ade-sede/ThumbsUp/src/movement.c

#include "header.h"
#include "MPU9150.h"
#include "movement.h"
#include "RN42.h"

extern struct s_accel g_calibration;
extern struct s_gravity g_accel;
extern struct s_gravity g_angle;

extern float g_accelR;
extern float g_wheel;

void    accel_to_angle_value() {
	/* accelometre value translate to g value between -/+2 */
	g_accel.accelX = TRANS_ACCEL_TO_G(g_calibration.accelX);
	g_accel.accelY = TRANS_ACCEL_TO_G(g_calibration.accelY);
	g_accel.accelZ = TRANS_ACCEL_TO_G(g_calibration.accelZ);

        /* Vector Acceleration R submitted to gravity */
	g_accelR = sqrt(powf(g_accel.accelX, 2.0) + powf(g_accel.accelY, 2.0) + powf(g_accel.accelZ, 2.0));

	/* Give angle in degrees of the vector */
	g_angle.accelX = acosf(g_accel.accelX/ g_accelR) * 57.2958;
	g_angle.accelY = acosf(g_accel.accelY/ g_accelR) * 57.2958;
	g_angle.accelZ = acosf(g_accel.accelZ/ g_accelR) * 57.2958;
}

/*	
 * This is the function that measures the forces present in the system, 	
 * during a no-move condition at the beginnig	
 * and shorter during execution	
 * We average those measures using calibration_sample_number samples	
 */

 void calibration(void) {	
	u16 count = 0;	
	struct s_accel sample_accel;
        LATBbits.LATB14 = 1;
 	while (count <= CALIBRATION_SAMPLE_NUMBER) {	
		memset(&sample_accel, 0, sizeof(struct s_accel));	
		read_accel(&sample_accel);	
		g_calibration.accelX += sample_accel.accelX;	
		g_calibration.accelY += sample_accel.accelY;	
		g_calibration.accelZ += sample_accel.accelZ;	
		++count;
	}	
 	g_calibration.accelX /= CALIBRATION_SAMPLE_NUMBER;	
	g_calibration.accelY /= CALIBRATION_SAMPLE_NUMBER;	
	g_calibration.accelZ /= CALIBRATION_SAMPLE_NUMBER;

        g_accel.accelX = TRANS_ACCEL_TO_G(g_calibration.accelX);
	g_accel.accelY = TRANS_ACCEL_TO_G(g_calibration.accelY);
	g_accel.accelZ = TRANS_ACCEL_TO_G(g_calibration.accelZ);
        LATBbits.LATB14 = 0;
}

void    sampling_acceleration_value() {
	u16 count = 0;
	struct s_accel sample;
        struct s_accel accel;

        memset(&accel, 0, sizeof(struct s_accel));
	/* SAMPLING */
	while (count <= AVERAGE_SAMPLE_NUMBER) {
		memset(&sample, 0, sizeof(struct s_accel));
		read_accel(&sample);
		accel.accelX += sample.accelX;
		accel.accelY += sample.accelY;
		accel.accelZ += sample.accelZ;
		++count;
	}
	/* Retrieving average */
	accel.accelX /= AVERAGE_SAMPLE_NUMBER;
	accel.accelY /= AVERAGE_SAMPLE_NUMBER;
	accel.accelZ /= AVERAGE_SAMPLE_NUMBER;

        /* giving value between -2 +2 */
	g_accel.accelX = TRANS_ACCEL_TO_G(accel.accelX);
	g_accel.accelY = TRANS_ACCEL_TO_G(accel.accelY);
	g_accel.accelZ = TRANS_ACCEL_TO_G(accel.accelZ);
}

void    angle_calculation(struct s_gravity *arcos){
//
//        float x = 0;
//        float y = 0;
//        float z = 0;

	g_accelR = sqrt(powf(g_accel.accelX, 2.0)+powf(g_accel.accelY, 2.0)+ powf(g_accel.accelZ, 2.0));

//        x = (g_accel.accelX - 1) * 9.81;
//        y = (g_accel.accelY - 1) * 9.81;
//        z = (g_accel.accelZ - 1) * 9.81;

//        print_accelR(g_accel.accelX * 100);
//        print_accelR(g_accel.accelY * 100);
//        print_accelR(g_accel.accelZ * 100);
        
	/* Give angle in degrees of the vector */
	arcos->accelX = acosf(g_accel.accelX/ g_accelR) * 57.2958;
	arcos->accelY = acosf(g_accel.accelY/ g_accelR) * 57.2958;
	arcos->accelZ = acosf(g_accel.accelZ/ g_accelR) * 57.2958;

	/* calibration */
	arcos->accelX -= g_angle.accelX;
	arcos->accelY -= g_angle.accelY;
	arcos->accelZ -= g_angle.accelZ;
}

void	movement(void) {
        struct s_gravity arcos;

        memset(&arcos, 0, sizeof(struct s_gravity));
        accel_to_angle_value();
        sampling_acceleration_value();
        angle_calculation(&arcos);

        //print_arcos(&arcos);
        /* Wheel */
        if (arcos.accelZ >= 110)
        {
            if(!(INVALID_VALUE(arcos.accelY)))
                g_wheel = arcos.accelY / 2;
            send_report(create_report(0, 0));
        }
        /* Movement */
        else
        {
            /*
            ** Interpret acceleration close to 0, as if they were 0
            ** Everything beetwen window _low and window_high is considered to be 0.
            ** Window_low is a negative integer, window_high a positive one
            */
            if (INVALID_VALUE(arcos.accelX) || arcos.accelX > 85)
               arcos.accelX = 0;
            if (INVALID_VALUE(arcos.accelY) || arcos.accelY > 85)
                arcos.accelY = 0;
            if (INVALID_VALUE(arcos.accelZ) || arcos.accelZ > 85)
                arcos.accelZ = 0;


            send_report(create_report(-arcos.accelX / 2, -arcos.accelY / 2));
        }
        /* Blink LED */
        if(LATBbits.LATB14 == 1 || !(arcos.accelY == 0 && arcos.accelX == 0))
            LATBbits.LATB14 ^= 1;

	/* Blank spot for new values */
	memset(&g_accel, 0, sizeof(struct s_accel));
        memset(&arcos, 0, sizeof(struct s_gravity));
        g_wheel = 0;
}
