ade-sede/ThumbsUp/src/config.c

// PIC32MX150F128B Configuration Bit Settings

// 'C' source line config statements

#include <xc.h>

// DEVCFG3
// USERID = No Setting
#pragma config PMDL1WAY = OFF           // Peripheral Module Disable Configuration (Allow multiple reconfigurations)
#pragma config IOL1WAY = OFF            // Peripheral Pin Select Configuration (Allow multiple reconfigurations)
#pragma config FUSBIDIO = OFF           // USB USID Selection (Controlled by Port Function)
#pragma config FVBUSONIO = OFF          // USB VBUS ON Selection (Controlled by Port Function)

// DEVCFG2
#pragma config FPLLIDIV = DIV_2         // PLL Input Divider (2x Divider)
#pragma config FPLLMUL = MUL_20         // PLL Multiplier (20x Multiplier)
#pragma config FPLLODIV = DIV_2         // System PLL Output Clock Divider (PLL Divide by 2)

// DEVCFG1
#pragma config FNOSC = FRCPLL           // Oscillator Selection Bits (Fast RC Osc with PLL)
#pragma config FSOSCEN = OFF            // Secondary Oscillator Enable (Disabled)
#pragma config IESO = OFF               // Internal/External Switch Over (Disabled)
#pragma config POSCMOD = OFF            // Primary Oscillator Configuration (Primary osc disabled)
#pragma config OSCIOFNC = OFF           // CLKO Output Signal Active on the OSCO Pin (Disabled)
#pragma config FPBDIV = DIV_2           // Peripheral Clock Divisor (Pb_Clk is Sys_Clk/2)
#pragma config FCKSM = CSDCMD           // Clock Switching and Monitor Selection (Clock Switch Disable, FSCM Disabled)
#pragma config WDTPS = PS1048576        // Watchdog Timer Postscaler (1:1048576)
#pragma config WINDIS = OFF             // Watchdog Timer Window Enable (Watchdog Timer is in Non-Window Mode)
#pragma config FWDTEN = OFF             // Watchdog Timer Enable (WDT Disabled (SWDTEN Bit Controls))
#pragma config FWDTWINSZ = WINSZ_25     // Watchdog Timer Window Size (Window Size is 25%)

// DEVCFG0
#pragma config JTAGEN = OFF             // JTAG Enable (JTAG Disabled)
#pragma config ICESEL = ICS_PGx1        // ICE/ICD Comm Channel Select (Communicate on PGEC1/PGED1)
#pragma config PWP = OFF                // Program Flash Write Protect (Disable)
#pragma config BWP = OFF                // Boot Flash Write Protect bit (Protection Disabled)
#pragma config CP = OFF                 // Code Protect (Protection Disabled)


/* Following this configuration,  SYSCLK is 80MHz and PBCLK is 40MHz */

/* IF ANY OF THOSE DEFINES ARE CHANGED YOU NEED TO ADJUST THE DEFINES IN CLOCK.H */

#undef SYSCLK
#define SYSCLK (8000000 / 2 * 20 / 2)

#undef PBCLK
#define PBCLK (SYSCLK / 2)
