ade-sede/ThumbsUp/src/RN42.c

#include "header.h"
#include "uart.h"
#include "MPU9150.h"
#include "interrupt.h"

/* bouton n = (1 << n) bouton indexe en 0
**/

/* Create generic report with Mouse data
**/
extern u8 g_button;
extern float g_wheel;

s16  *create_report(s16 x_move, s16 y_move) {
    s16 static report[7];
    u16 pot = pot_report();
    // If you want activate sensibily with potentiometre add pot variable to report[4] and [5]

        memset(report, 0, sizeof(s16) * 7);
	report[0] = (s16)0xFD; // Format mouse raw
	report[1] = (s16)5; // Length
	report[2] = (s16)2; // Data descriptor -> Mouse
	report[3] = (s16)g_button;
	report[4] = (s16)(x_move) * (pot / 300.0);// * pot;
	report[5] = (s16)(y_move) * (pot / 300.0);// * pot;
	report[6] = (s16)g_wheel * (pot > 100 ? 1 : 0); // Wheel
        print_report(report);

        if (g_button > 1 || (TRISAbits.TRISA2 == 0 && g_button == 1))
            g_button = 0;
	return (report);
}

/*
** Send Mouse raw report format to module bluetooth
** Sending protocol should never be interrupted ! Therefor, CPU interrupt state
** is jumped to the highest, and restored to its original state when sending is over 
*/

void send_report(s16 *report) {
	u16 i = 0;
	unsigned int original_priority;

	/* Storing priority on entry, jumping to highest */
	original_priority = __builtin_get_isr_state();
	__builtin_set_isr_state(7);
	while (i < 7) {
		uart1_transmit_idle(report[i]);
		i++;
	}
	while (i < 5000)
		++i;
	Nop();
	/* Restoring priority */
	__builtin_set_isr_state(original_priority);
}
