ade-sede/ThumbsUp/src/uart2.c

#include "header.h"
#include "uart.h"

void uart2_transmit_byte(u8 byte) {
    while (U2STAbits.UTXBF); // If transmit buffer is not full
    U2TXREG = byte; // Fill transmit buffer;
}

void uart2_idle_after_transmit() {
    while (U2STAbits.TRMT != 1); // Transmit idle
}

u8 uart2_receive_byte(){
    if (U2STAbits.URXDA)
        return(U2RXREG);
}

void uart2_transmit_idle(u8 byte) {
    uart2_transmit_byte(byte);
    uart2_idle_after_transmit();
}

void uart2_init(u32 BRG){
    U2BRG = BRG; // Target baude rate = 115k
    U2MODEbits.BRGH = 0;
    U2MODEbits.PDSEL = 0; // 8 bit data, no parity
    U2MODEbits.STSEL = 0; // 1 stop bits
    U2STAbits.URXEN = 1; // reception enable
    U2STAbits.UTXEN = 1; // Transmition enabled.
    U2MODEbits.ON = 1;
}

void uart2_putstr(u8 *str) {
	while(*str){
		uart2_transmit_byte(*str);
		++str;
	}
	uart2_idle_after_transmit();
}
