ade-sede/ThumbsUp/src/i2c.h

/* 
 * File:   i2c.h
 * Author: bocal
 *
 * Created on July 13, 2018, 4:17 PM
 */

#ifndef I2C_H
# define I2C_H
# include "MPU9150.h"

#ifndef PBCLK
# include "clock.h"
#endif
#define FSCK 4000 // 400kHz
#define I2CBRG (PBCLK / (2 * FSCK)) - 2

#define RW_READ 1
#define RW_WRITE 0
#define ADDR_READ_MODE(addr) ((addr << 1) | RW_READ)
#define ADDR_WRITE_MODE(addr) (addr << 1)
#define NACK 1
#define ACK 0

/* Prototypes */
void i2c_config_and_start(u8 brg);
void i2c_master_send(u8 data);
void i2c_master_receive(u8 *dest);
void i2c_master_answer(u8 value);


#endif	/* I2C_H */
